nwsteenberg/NWSplit/firmware/nwsplit/keymaps/default/keymap.c

#include QMK_KEYBOARD_H

enum layer_names {
    _QWERTY,
    _LAYER1,
    _LAYER2,
    _POINTER
};

#define L_1 MO(_LAYER1)
#define L_2 MO(_LAYER2)
#define L_P MO(_POINTER)
#define CTL_ESC LCTL_T(KC_ESC)

const uint16_t PROGMEM keymaps[][MATRIX_ROWS][MATRIX_COLS] = {
    [_QWERTY] = LAYOUT(
        KC_MPLY,                                                                                          
        KC_TAB,  KC_1,    KC_2,    KC_3,    KC_4,    KC_5,                    KC_6,    KC_7,    KC_8,    KC_9,    KC_0,    KC_MINUS,
        CTL_ESC, KC_Q,    KC_W,    KC_E,    KC_R,    KC_T,                    KC_Y,    KC_U,    KC_I,    KC_O,    KC_P,    KC_LBRC, 
        KC_LSFT, KC_A,    KC_S,    KC_D,    KC_F,    KC_G,                    KC_H,    KC_J,    KC_K,    KC_L,    KC_SCLN, KC_QUOT, 
                 KC_Z,    KC_X,    KC_C,    KC_V,    KC_B,                    KC_N,    KC_M,    KC_COMM, KC_DOT,  KC_SLSH,     
                                           KC_LALT, KC_SPC,  L_1,    KC_ENT,  KC_BSPC, KC_RALT
    ),

    [_LAYER1] = LAYOUT(
        KC_TRNS,                                                                                          
        KC_TRNS, KC_TRNS,      KC_TRNS,      KC_TRNS,      KC_TRNS,      KC_TRNS,     KC_TRNS, KC_TRNS, KC_TRNS, KC_TRNS, KC_TRNS,       KC_EQL,  
        KC_TRNS, KC_1,         KC_2,         KC_3,         KC_4,         KC_5,        KC_6,    KC_7,    KC_8,    KC_9,    KC_0,          KC_RBRC,  
        KC_TRNS, ALGR(KC_EQL), LSFT(KC_SLSH), ALGR(KC_7),   ALGR(KC_0),   ALGR(KC_4),  KC_LEFT, KC_DOWN, KC_UP,   KC_RGHT, ALGR(KC_RBRC), KC_BSLS,  
                 KC_NUBS,      ALGR(KC_NUBS),ALGR(KC_8),   ALGR(KC_9),   LSFT(KC_BSLS),KC_HOME,KC_PGDN, KC_PGUP, KC_END,  KC_TRNS, 
                                           KC_TRNS, KC_TRNS, KC_TRNS, KC_INS,  KC_DEL, L_2 
    ),

    [_LAYER2] = LAYOUT(
        KC_TRNS,                                                                                          
        KC_F1,   KC_F2,   KC_F3,   KC_F4,   KC_F5,   KC_F6,                   KC_F7,   KC_F8,   KC_F9,   KC_F10,  KC_F11,  KC_F12,  
        KC_TRNS, KC_TRNS, KC_TRNS, KC_TRNS, KC_TRNS, KC_TRNS,                 KC_TRNS, KC_TRNS, KC_TRNS, KC_TRNS, KC_TRNS, KC_TRNS,  
        KC_TRNS, KC_TRNS, KC_TRNS, KC_TRNS, KC_TRNS, KC_TRNS,                 KC_TRNS, KC_TRNS, KC_TRNS, KC_TRNS, KC_TRNS, KC_TRNS,  
                 KC_TRNS, KC_TRNS, KC_TRNS, KC_TRNS, KC_TRNS,                 KC_TRNS, KC_TRNS, KC_TRNS, KC_TRNS, KC_TRNS, 
                                           KC_TRNS, KC_TRNS, KC_TRNS, KC_TRNS, KC_TRNS, KC_TRNS
    ),

    [_POINTER] = LAYOUT(
        KC_BTN3,                                                                                          
        KC_TRNS, KC_TRNS, KC_TRNS, KC_TRNS, KC_TRNS, KC_TRNS,                 KC_TRNS, KC_TRNS, KC_TRNS, KC_TRNS, KC_TRNS, KC_TRNS,  
        KC_TRNS, KC_TRNS, KC_TRNS, KC_TRNS, KC_TRNS, KC_TRNS,                 KC_TRNS, KC_TRNS, KC_TRNS, KC_TRNS, KC_TRNS, KC_TRNS,  
        KC_TRNS, KC_TRNS, KC_TRNS, KC_TRNS, KC_TRNS, KC_TRNS,                 KC_TRNS, KC_TRNS, KC_TRNS, KC_TRNS, KC_TRNS, KC_TRNS,  
                 KC_TRNS, KC_TRNS, KC_TRNS, KC_TRNS, KC_TRNS,                 KC_TRNS, KC_TRNS, KC_TRNS, KC_TRNS, KC_TRNS, 
                                           KC_BTN1, KC_BTN3, KC_BTN2, KC_TRNS, KC_TRNS, KC_TRNS
    )
};

#if defined(ENCODER_MAP_ENABLE)
const uint16_t PROGMEM encoder_map[][NUM_ENCODERS][2] = {
    [0] = { ENCODER_CCW_CW(KC_VOLU, KC_VOLD) },
    [1] = { ENCODER_CCW_CW(KC_TRNS, KC_TRNS) },
    [2] = { ENCODER_CCW_CW(KC_TRNS, KC_TRNS) },
    [3] = { ENCODER_CCW_CW(MS_WHLU, MS_WHLD) },
};
#endif
